mdavydau/bobik/firmware/src/idle01.h

// idle01 animation for Adafruit SSD1306
// Generated from video - 97 frames @ 12fps
// Format: Adafruit_GFX bitmap (MSB first)
// Display: 128x64 OLED

#ifndef IDLE01_H
#define IDLE01_H

#include <Arduino.h>

// Animation properties
#define IDLE01_FRAME_COUNT 97
#define IDLE01_FPS 12
#define IDLE01_FRAME_DELAY 83  // ms per frame

// Frame data lives in idle01.cpp (separate translation unit for fast rebuilds)
extern const unsigned char* const idle01_frames[];

#endif
