mdavydau/bobik/firmware/src/startup01.h

// startup01 animation for Adafruit SSD1306
// Generated from video - 53 frames @ 8fps
// Format: Adafruit_GFX bitmap (MSB first)
// Display: 128x64 OLED

#ifndef STARTUP01_H
#define STARTUP01_H

#include <Arduino.h>

// Animation properties
#define STARTUP01_FRAME_COUNT 53
#define STARTUP01_FPS 8
#define STARTUP01_FRAME_DELAY 125  // ms per frame

// Frame data lives in startup01.cpp (separate translation unit for fast rebuilds)
extern const unsigned char* const startup01_frames[];

#endif
